Teodor04/InkTime_TSC/Images/pcb2dc63.png

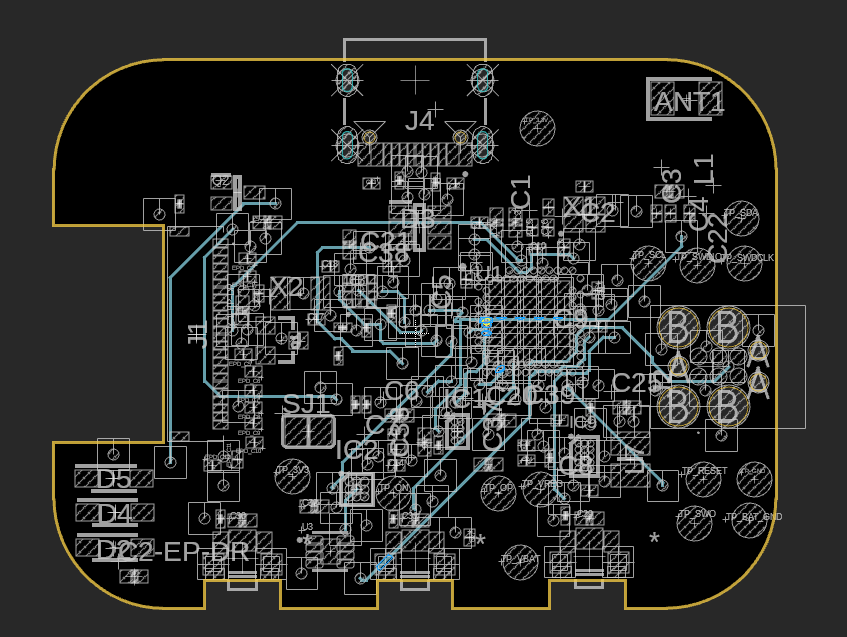
Images/pcb2dc63.png
